Skylakc/Plasma-Toroid/imgs/000.jpg

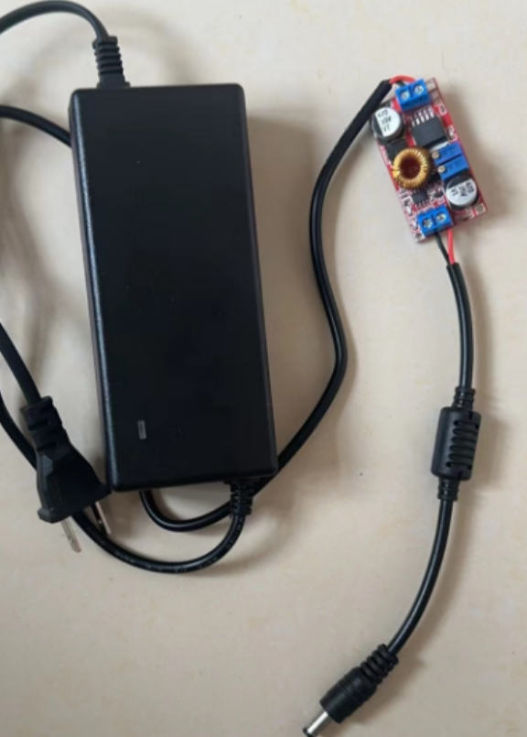
imgs/000.jpg
