Skylakc/Plasma-Toroid/imgs/1726911840947.jpg

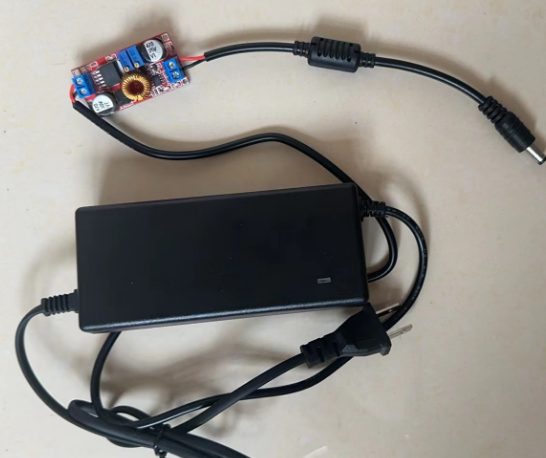
imgs/1726911840947.jpg
