Skylakc/Plasma-Toroid/imgs/c8e2e2199d0ae38854192d13ec5ad0f.jpg

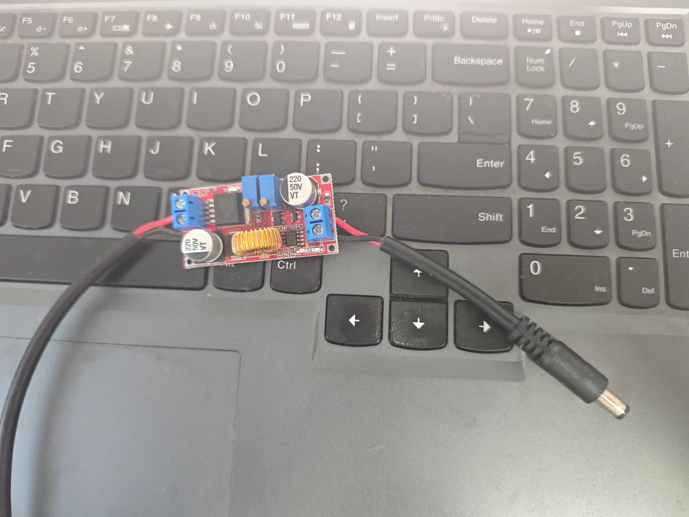
imgs/c8e2e2199d0ae38854192d13ec5ad0f.jpg
