Skylakc/Plasma-Toroid/imgs/imgs_24_3_1/sch_new.jpg

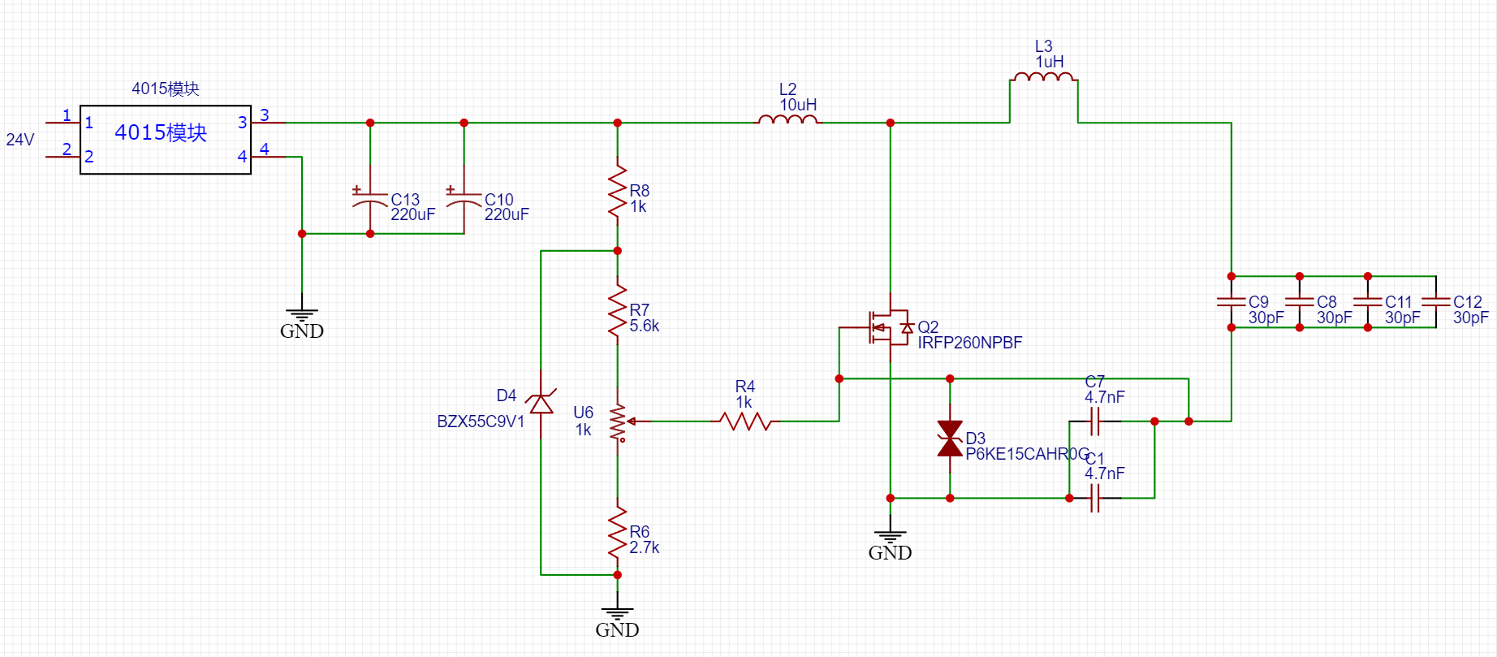
imgs/imgs_24_3_1/sch_new.jpg
