Skylakc/Plasma-Toroid/imgs/imgs_24_4_13/Coil3.JPG

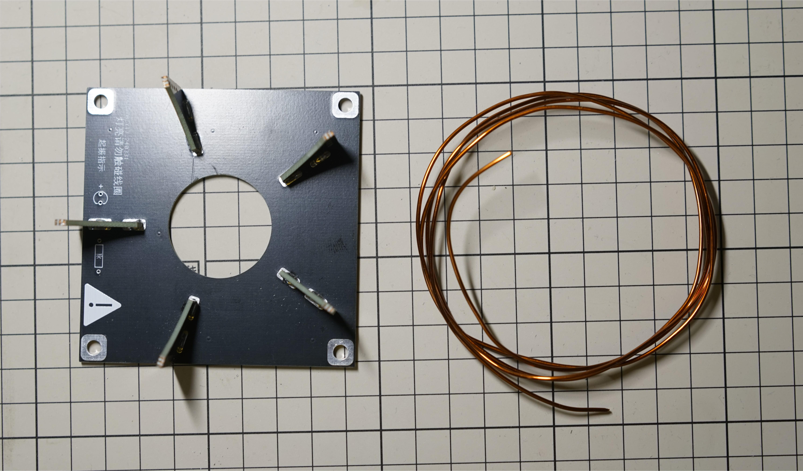
imgs/imgs_24_4_13/Coil3.JPG
