Skylakc/Plasma-Toroid/imgs/imgs_24_4_13/compress/Done.jpg

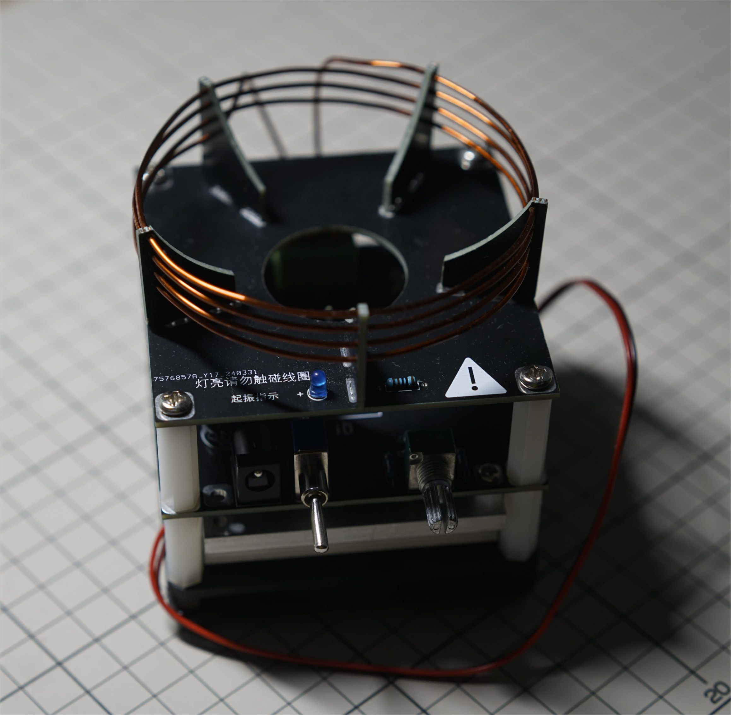
imgs/imgs_24_4_13/compress/Done.jpg
