Skylakc/Plasma-Toroid/imgs/imgs_24_4_13/compress/Ring.png

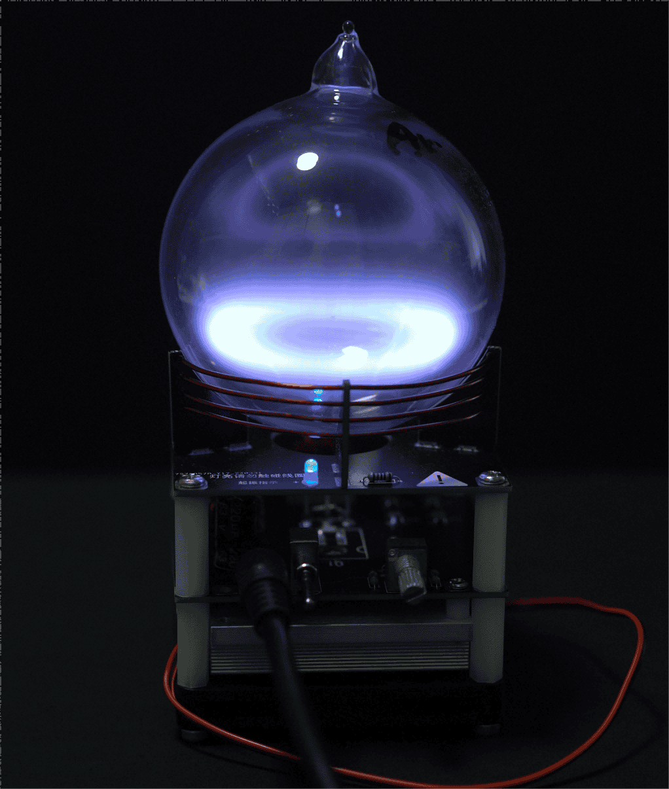
imgs/imgs_24_4_13/compress/Ring.png
