Skylakc/Plasma-Toroid/imgs/imgs_24_4_13/Fan1.JPG

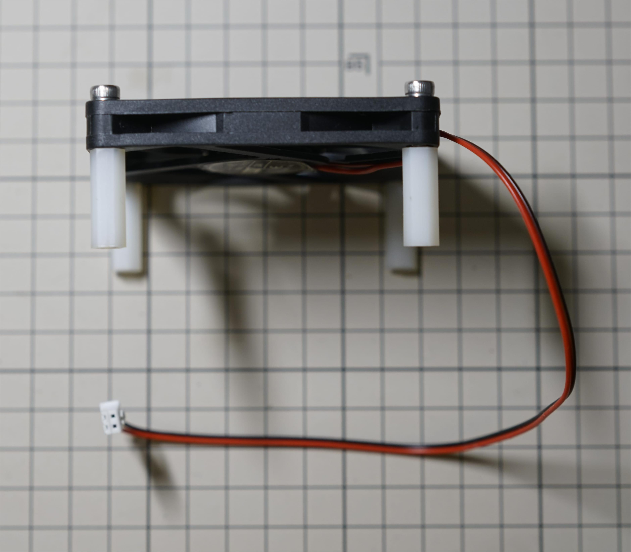
imgs/imgs_24_4_13/Fan1.JPG
