Skylakc/Plasma-Toroid/imgs/imgs_24_4_13/Fan2.JPG

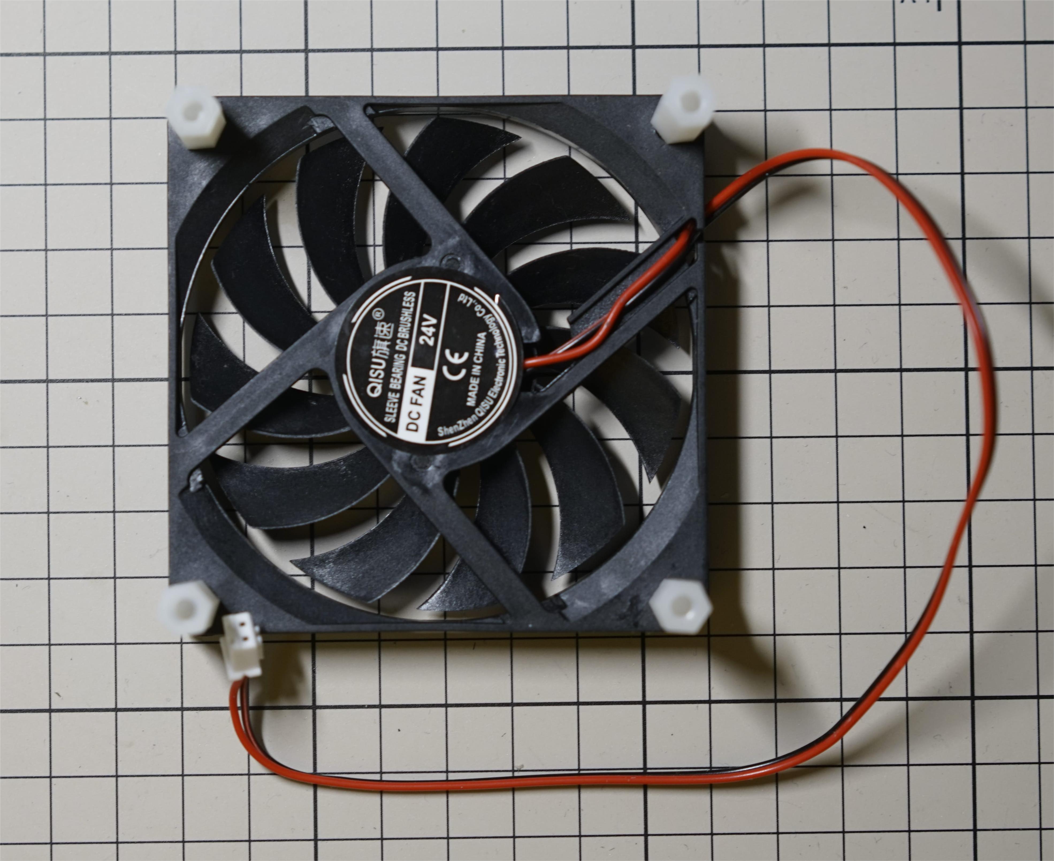
imgs/imgs_24_4_13/Fan2.JPG
