Skylakc/Plasma-Toroid/imgs/imgs_24_4_13/Heatsink0.JPG

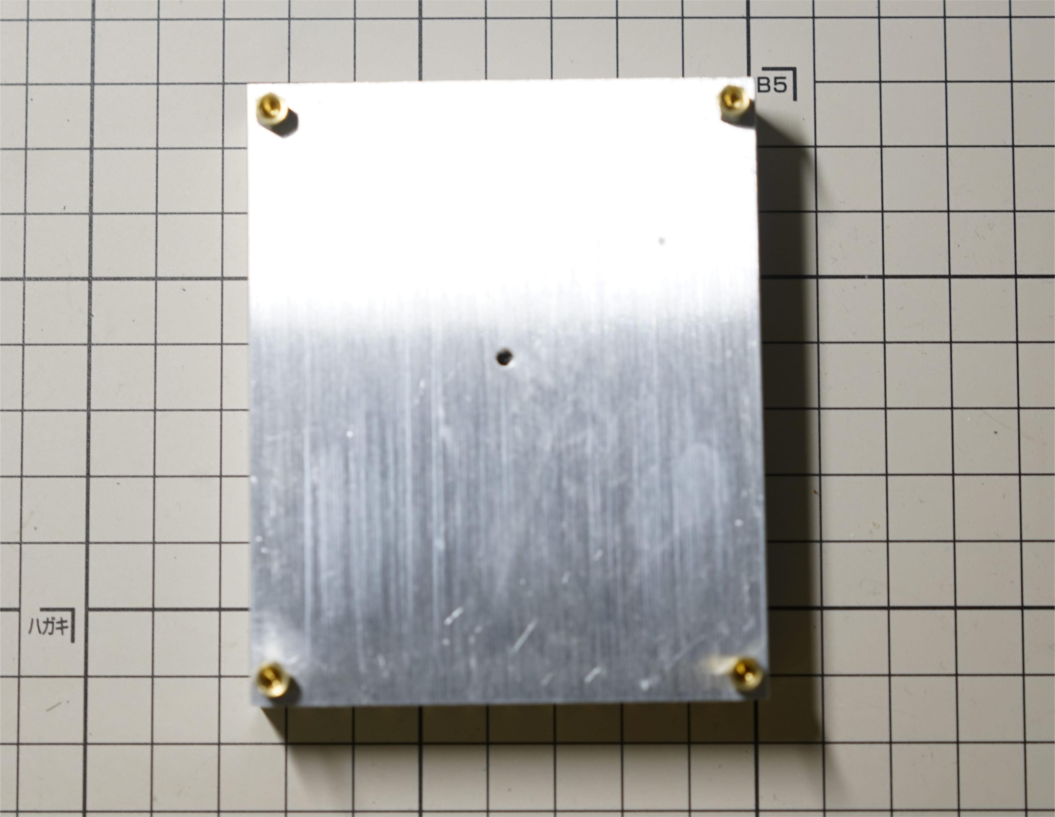
imgs/imgs_24_4_13/Heatsink0.JPG
