Skylakc/Plasma-Toroid/imgs/imgs_24_6_3/asemble_front.jpg

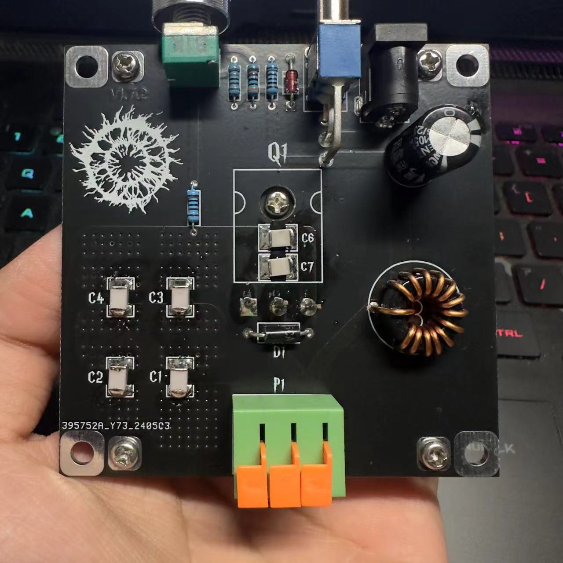
imgs/imgs_24_6_3/asemble_front.jpg
