Skylakc/Plasma-Toroid/imgs/imgs_24_6_3/微信图片_20240603215352.jpg

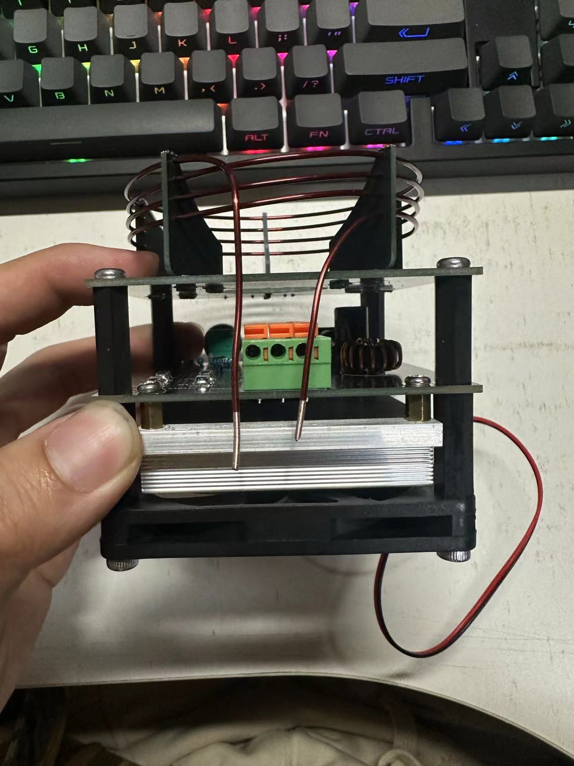
imgs/imgs_24_6_3/微信图片_20240603215352.jpg
