Skylakc/Plasma-Toroid/imgs/imgs_24_4_13/Assemble4.JPG

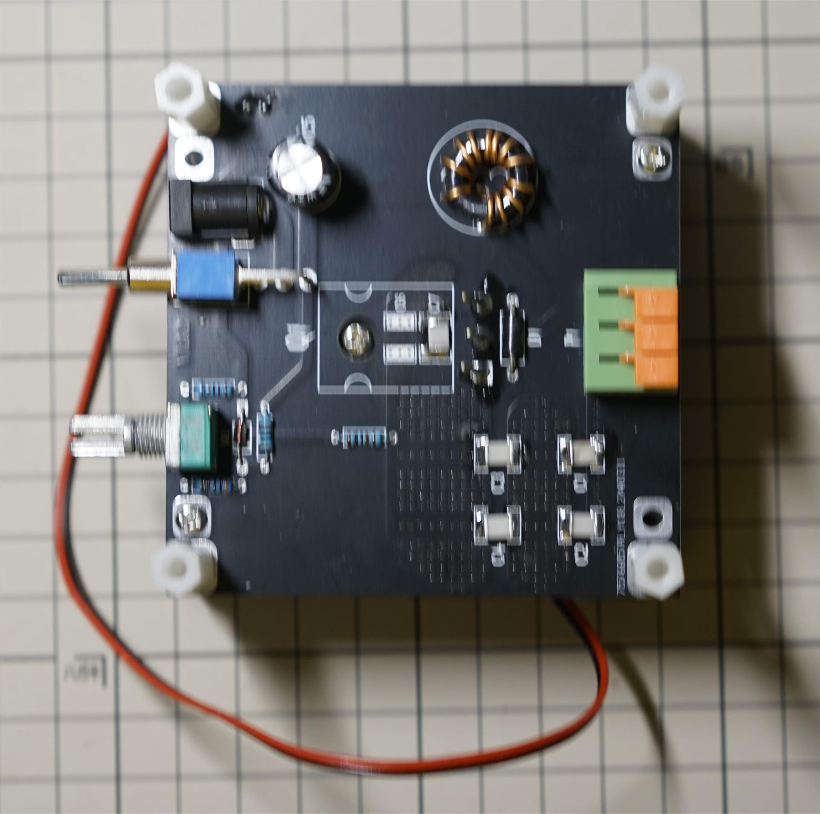
imgs/imgs_24_4_13/Assemble4.JPG
