Skylakc/Plasma-Toroid/imgs/imgs_24_4_13/Assemble6.JPG

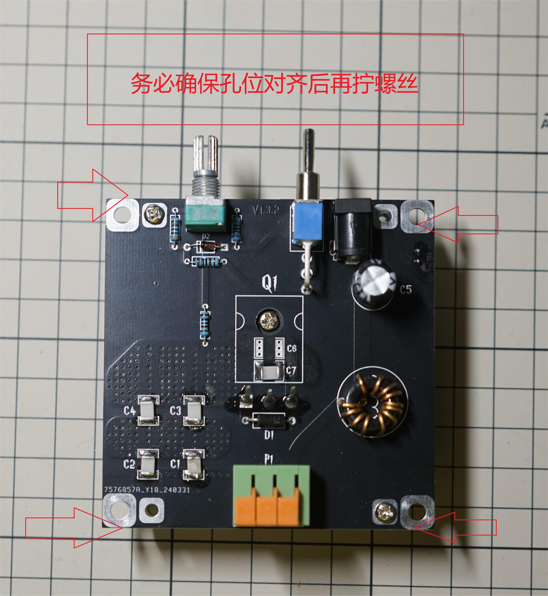
imgs/imgs_24_4_13/Assemble6.JPG
